Dawwen/PolyBoy/src/Psvita/sce_sys/livearea/contents/bg.png

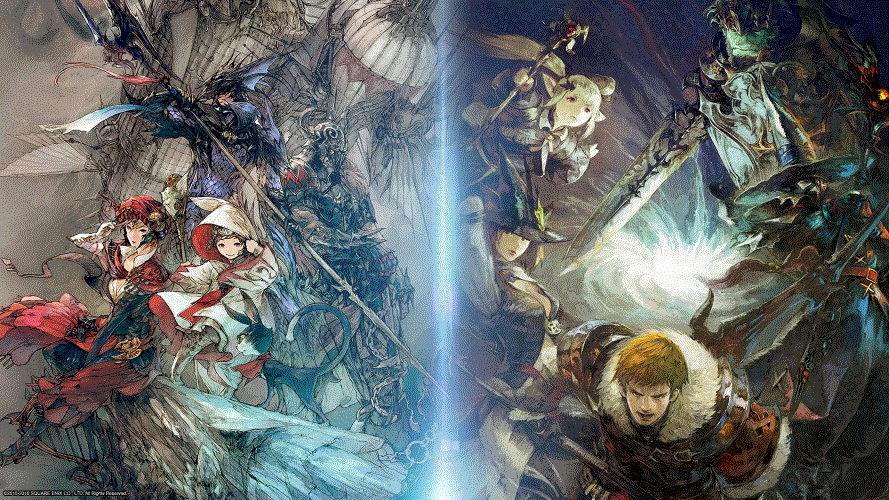
src/Psvita/sce_sys/livearea/contents/bg.png
