Dawwen/PolyBoy/src/Psvita/sce_sys/livearea/contents/startup.png

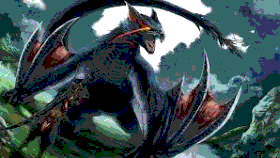
src/Psvita/sce_sys/livearea/contents/startup.png
