Dawwen/PolyBoy/models/Arduino Due/MicroUSB B - Hirose - ZX62D-B-5P8.SLDPRT

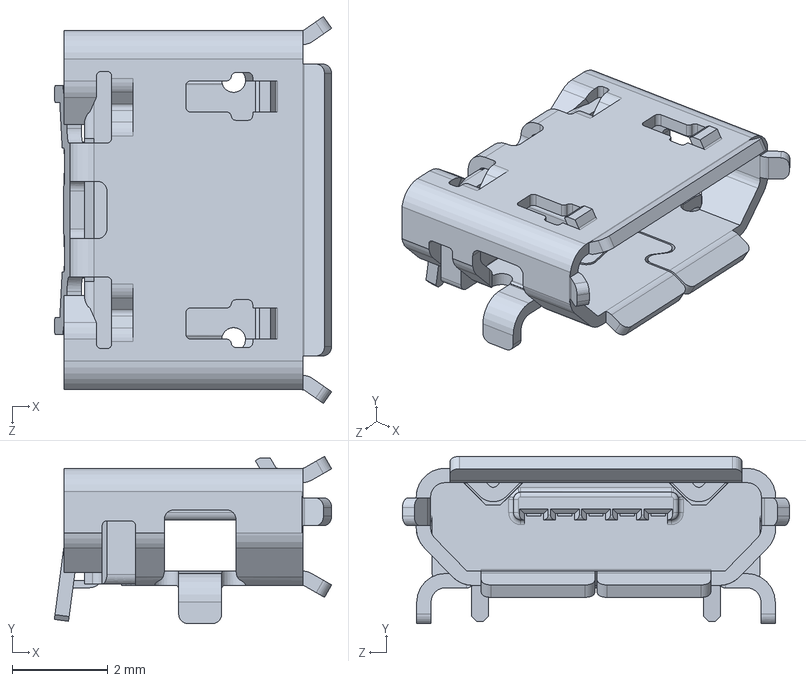
[picture p90: CAD file, 2021-04-26]
models/Arduino Due/MicroUSB B - Hirose - ZX62D-B-5P8.SLDPRT
5.80 x 3.50 x 8.09 mm
