Dawwen/PolyBoy/models/Entretoise10mm.SLDPRT

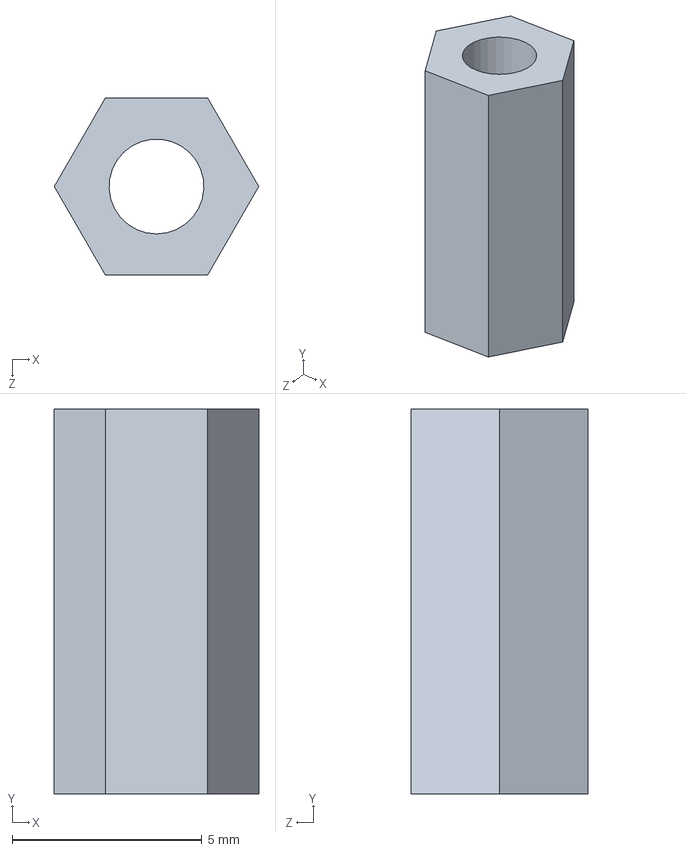
[picture p91: CAD file, 2021-04-26]
models/Entretoise10mm.SLDPRT
5.39 x 10.2 x 4.67 mm
