Dawwen/PolyBoy/models/Arduino Due/LED - Kingbright - KPT-3216EC.SLDPRT

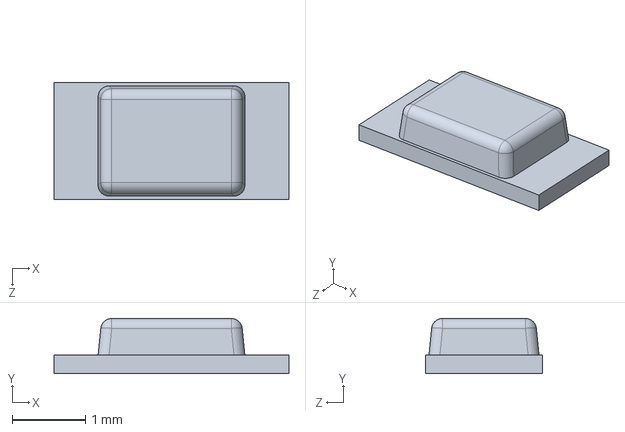
[picture p92: CAD file, 2021-04-26]
models/Arduino Due/LED - Kingbright - KPT-3216EC.SLDPRT
3.20 x 0.75 x 1.60 mm
