Dawwen/PolyBoy/models/PlaqueDPad.SLDPRT

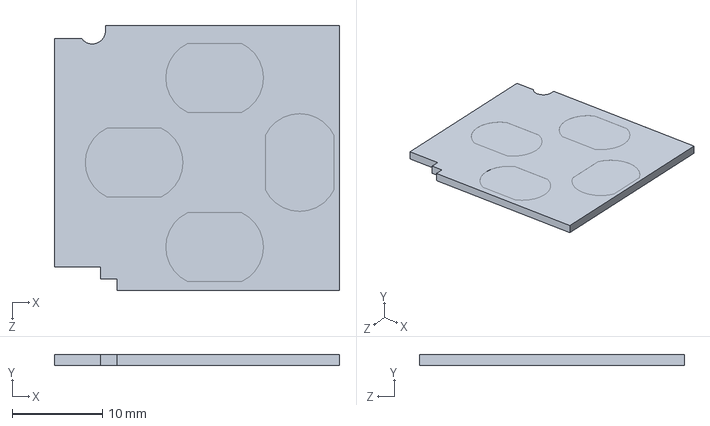
[picture p93: CAD file, 2021-04-26]
models/PlaqueDPad.SLDPRT
31.5 x 1.20 x 29.3 mm
