Dawwen/PolyBoy/models/Arduino Due/Switch - ESwitch - TLE3303.SLDPRT

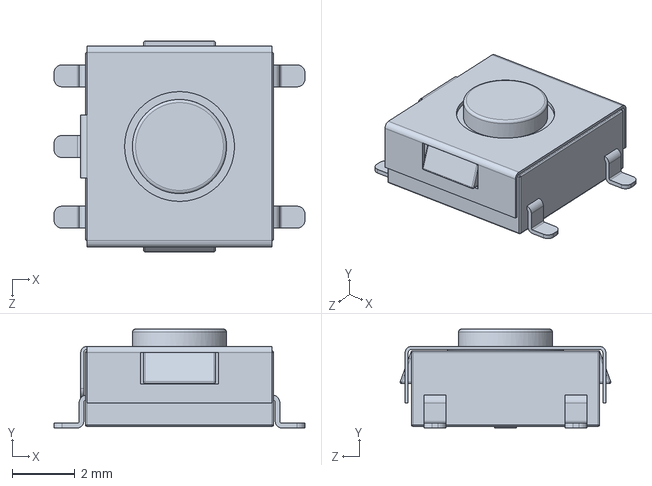
[picture p94: CAD file, 2021-04-26]
models/Arduino Due/Switch - ESwitch - TLE3303.SLDPRT
8.00 x 3.15 x 6.71 mm
