Dawwen/PolyBoy/models/BoitierHaut.SLDPRT

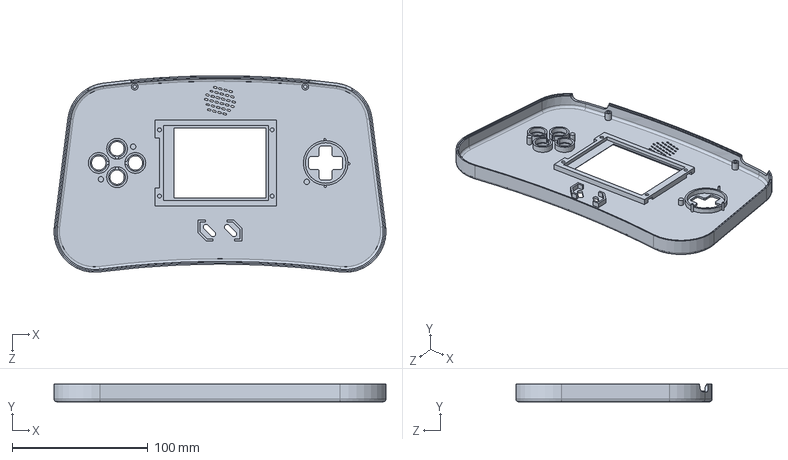
[picture p95: CAD file, 2021-04-26]
models/BoitierHaut.SLDPRT
245.0 x 13.0 x 145.0 mm
