Dawwen/PolyBoy/models/Arduino Due/Berg Header - 2.54 x 2.SLDPRT

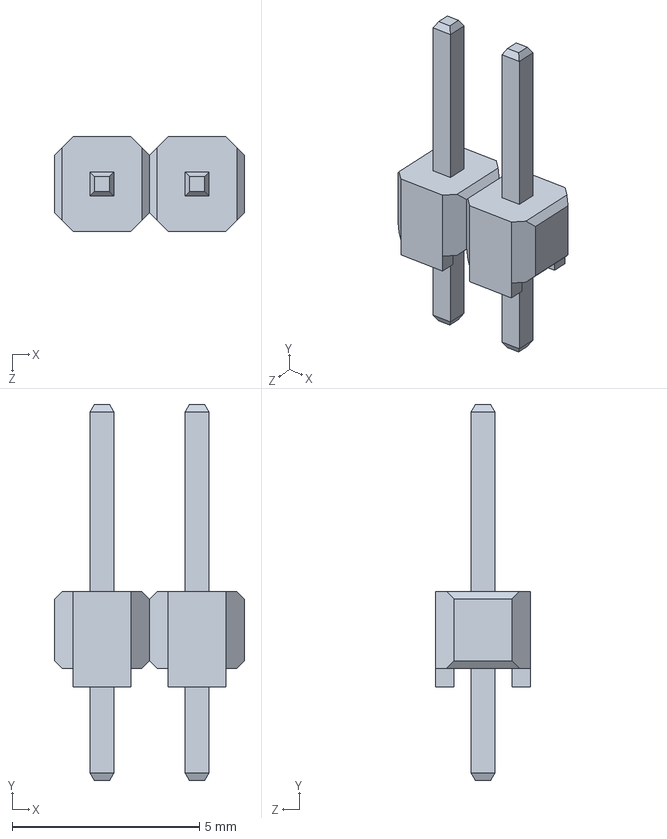
[picture p96: CAD file, 2021-04-26]
models/Arduino Due/Berg Header - 2.54 x 2.SLDPRT
5.08 x 10.0 x 2.54 mm
