Dawwen/PolyBoy/models/PlaqueGachette1.SLDPRT

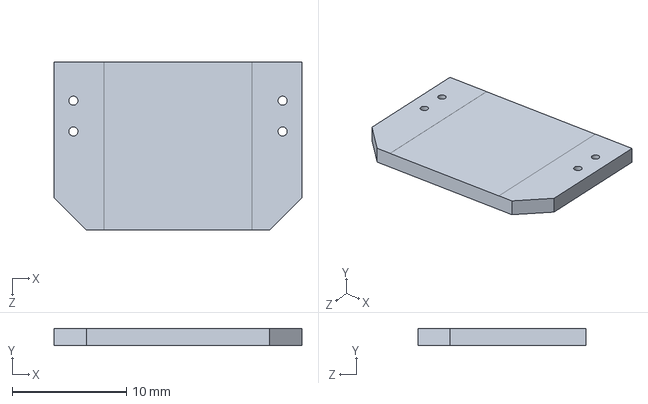
[picture p97: CAD file, 2021-04-26]
models/PlaqueGachette1.SLDPRT
21.8 x 1.50 x 14.8 mm
