Dawwen/PolyBoy/models/Arduino Due/MicroUSB AB - Hirose - ZX62D-AB-5P8.SLDPRT

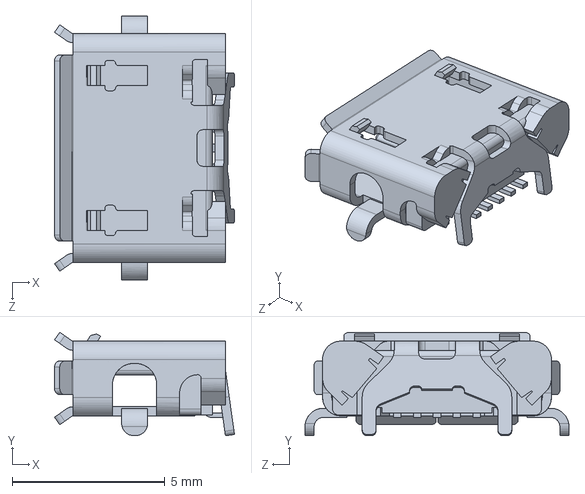
[picture p98: CAD file, 2021-04-26]
models/Arduino Due/MicroUSB AB - Hirose - ZX62D-AB-5P8.SLDPRT
5.90 x 3.39 x 8.65 mm
