Dawwen/PolyBoy/models/Entretoise8mm.SLDPRT

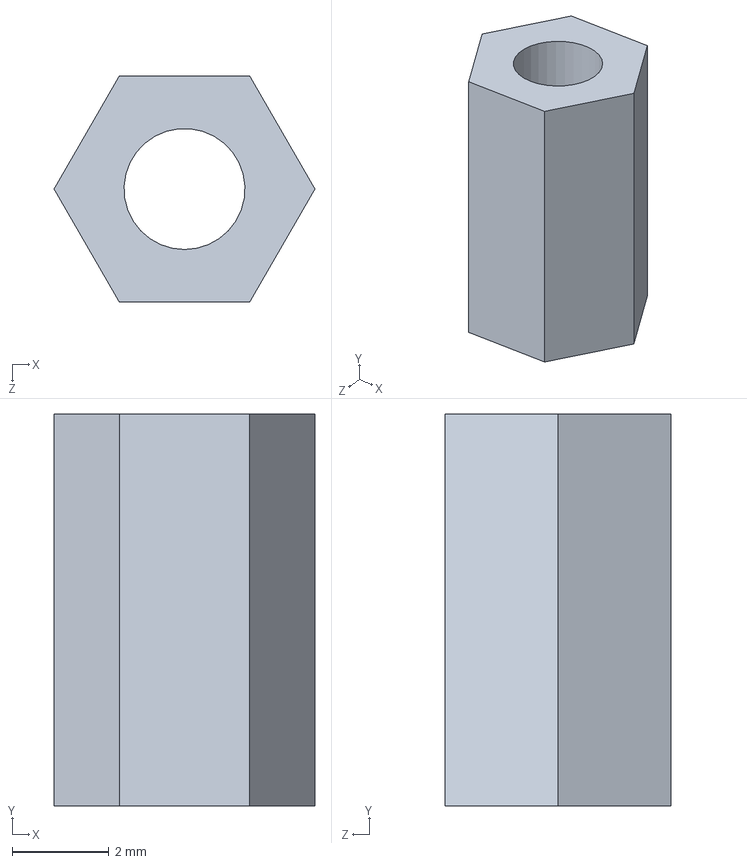
[picture p99: CAD file, 2021-04-26]
models/Entretoise8mm.SLDPRT
5.39 x 8.10 x 4.67 mm
