Dawwen/PolyBoy/models/Arduino Due/Berg Header Receptacle 2.54 x 10 - FCI - 66951-010LF.SLDPRT

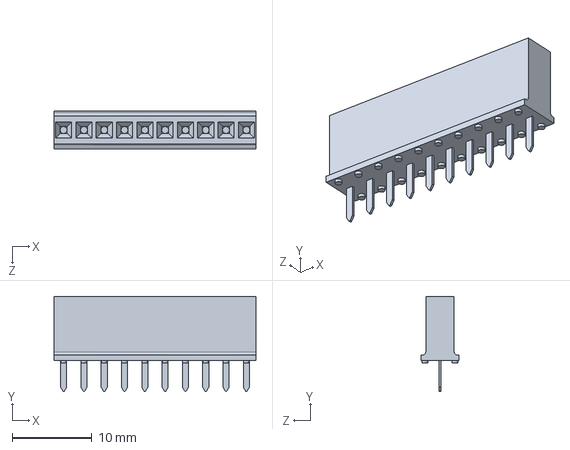
[picture p100: CAD file, 2021-04-26]
models/Arduino Due/Berg Header Receptacle 2.54 x 10 - FCI - 66951-010LF.SLDPRT
25.3 x 11.9 x 4.78 mm
