Dawwen/PolyBoy/models/PlaqueABXY.SLDPRT

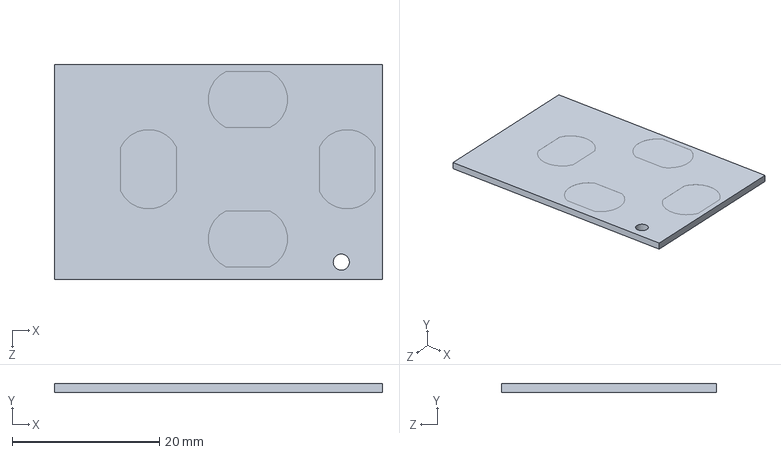
[picture p101: CAD file, 2021-04-26]
models/PlaqueABXY.SLDPRT
44.6 x 1.20 x 29.3 mm
