Dawwen/PolyBoy/models/Boulon.SLDPRT

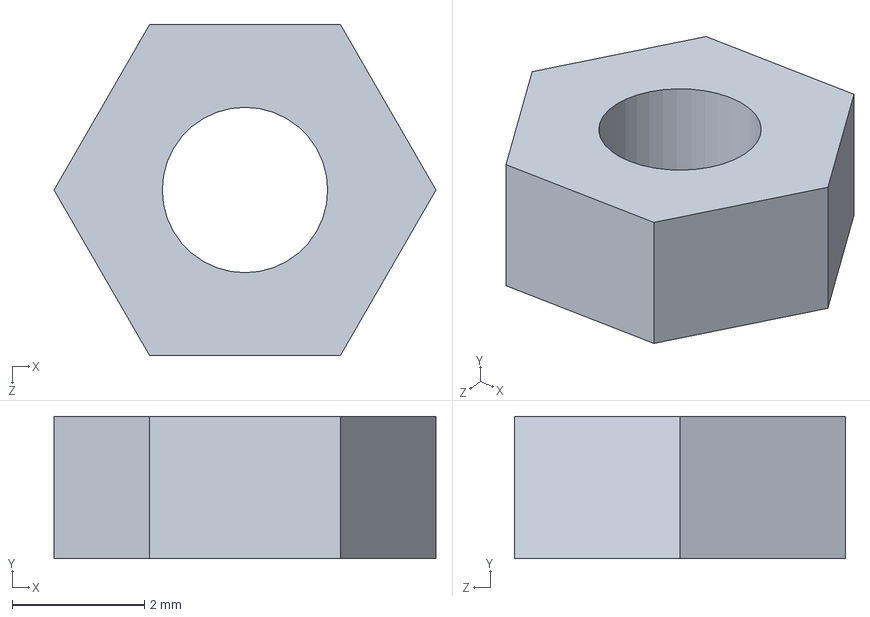
[picture p103: CAD file, 2021-04-26]
models/Boulon.SLDPRT
5.77 x 2.15 x 5.00 mm
