Dawwen/PolyBoy/models/Arduino Due/PCB - Arduino.SLDPRT

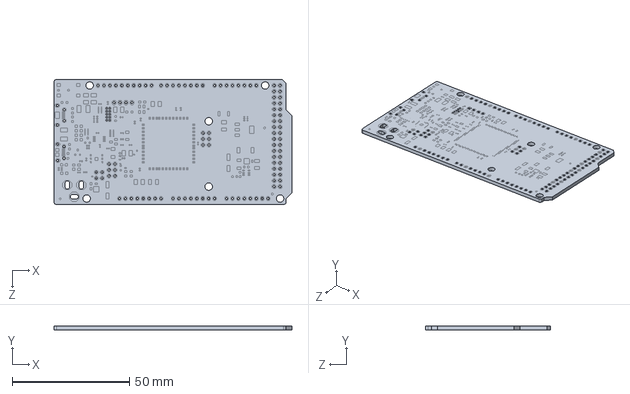
[picture p104: CAD file, 2021-04-26]
models/Arduino Due/PCB - Arduino.SLDPRT
101.6 x 1.62 x 53.3 mm
