Dawwen/PolyBoy/models/PlaqueStart.SLDPRT

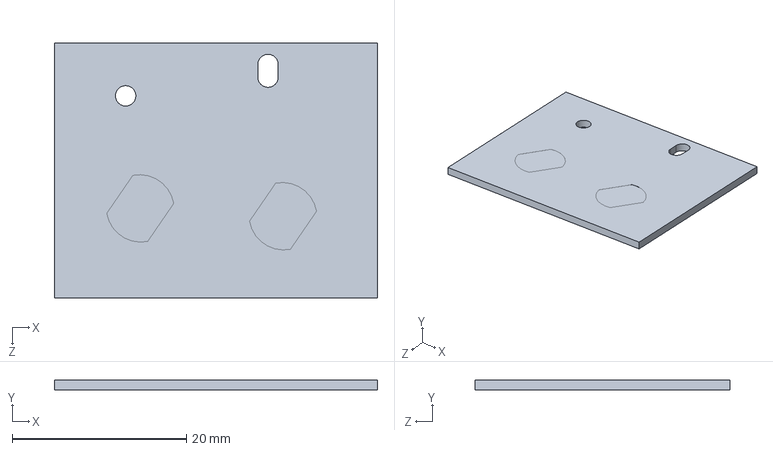
[picture p105: CAD file, 2021-04-26]
models/PlaqueStart.SLDPRT
37.1 x 1.20 x 29.3 mm
