Dawwen/PolyBoy/models/Arduino Due/Berg Header - 1.27 x 10.SLDPRT

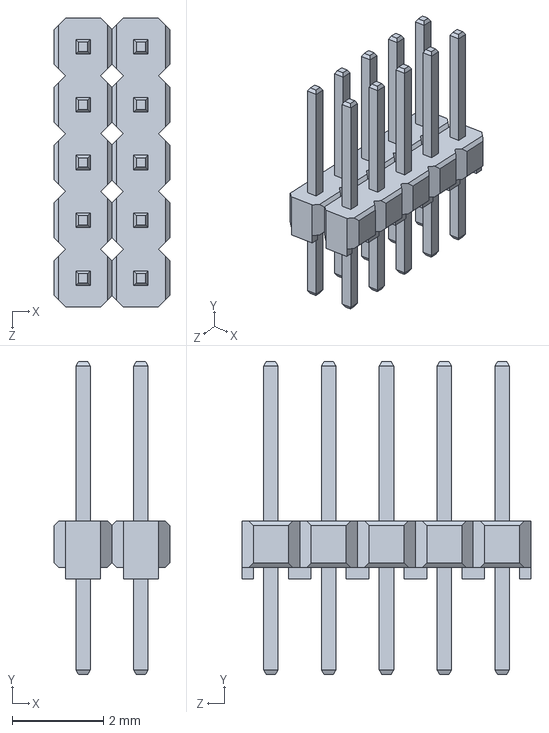
[picture p106: CAD file, 2021-04-26]
models/Arduino Due/Berg Header - 1.27 x 10.SLDPRT
2.54 x 6.88 x 6.35 mm
