Dawwen/PolyBoy/models/Vis14mm.SLDPRT

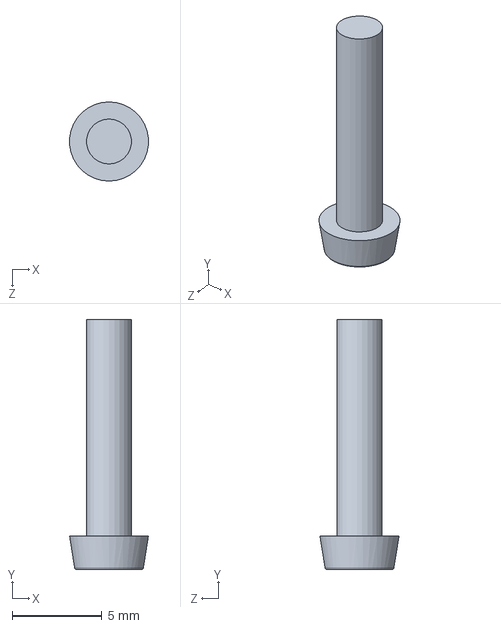
[picture p107: CAD file, 2021-04-26]
models/Vis14mm.SLDPRT
4.38 x 13.9 x 4.40 mm
