Dawwen/PolyBoy/models/MembraneDPad.SLDPRT

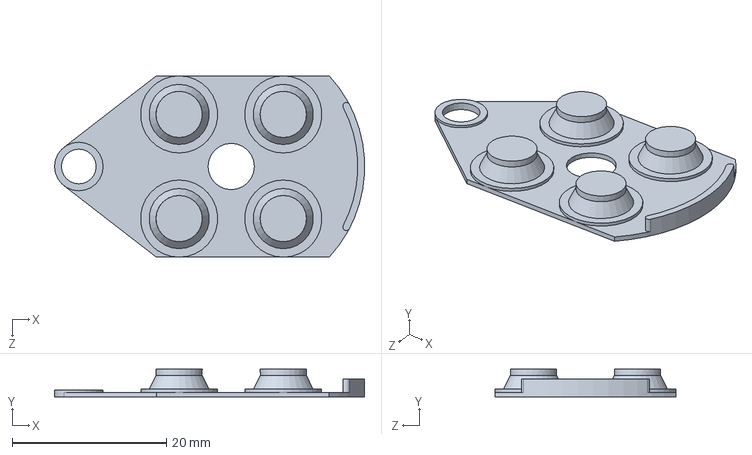
[picture p108: CAD file, 2021-04-26]
models/MembraneDPad.SLDPRT
40.2 x 3.60 x 23.5 mm
