Dawwen/PolyBoy/models/Entretoise20mm.SLDPRT

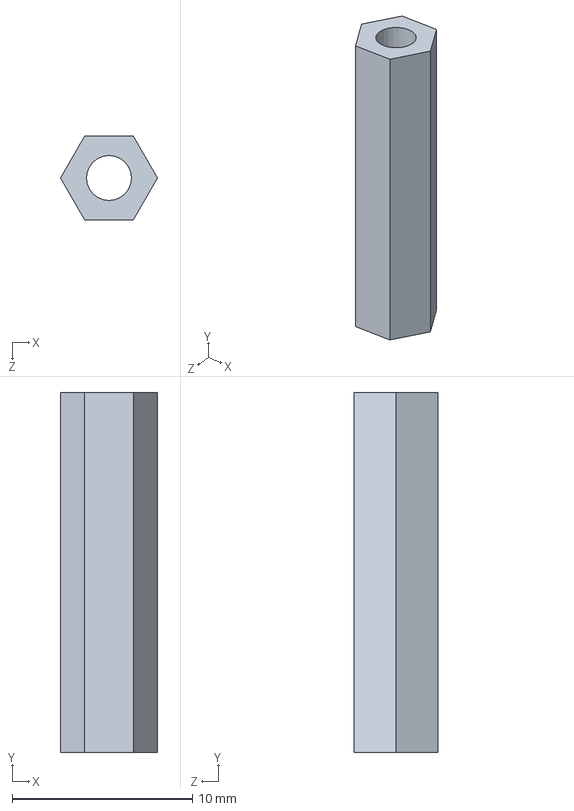
[picture p109: CAD file, 2021-04-26]
models/Entretoise20mm.SLDPRT
5.39 x 20.0 x 4.67 mm
