Dawwen/PolyBoy/models/Bouton.SLDPRT

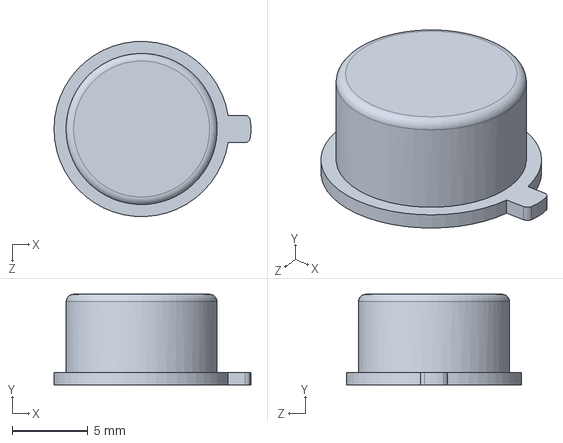
[picture p110: CAD file, 2021-04-26]
models/Bouton.SLDPRT
13.0 x 6.00 x 11.6 mm
