Dawwen/PolyBoy/models/PlaqueGachette2.SLDPRT

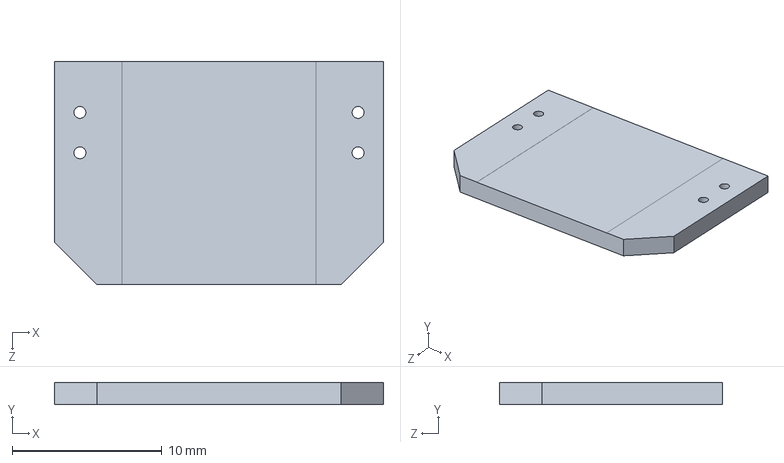
[picture p111: CAD file, 2021-04-26]
models/PlaqueGachette2.SLDPRT
22.0 x 1.50 x 14.9 mm
