Dawwen/PolyBoy/models/Entretoise12mm.SLDPRT

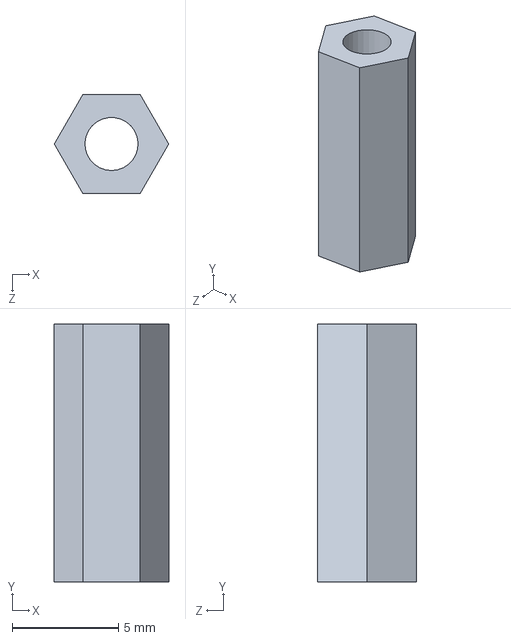
[picture p112: CAD file, 2021-04-26]
models/Entretoise12mm.SLDPRT
5.39 x 12.1 x 4.67 mm
