Dawwen/PolyBoy/models/Ecran.SLDPRT

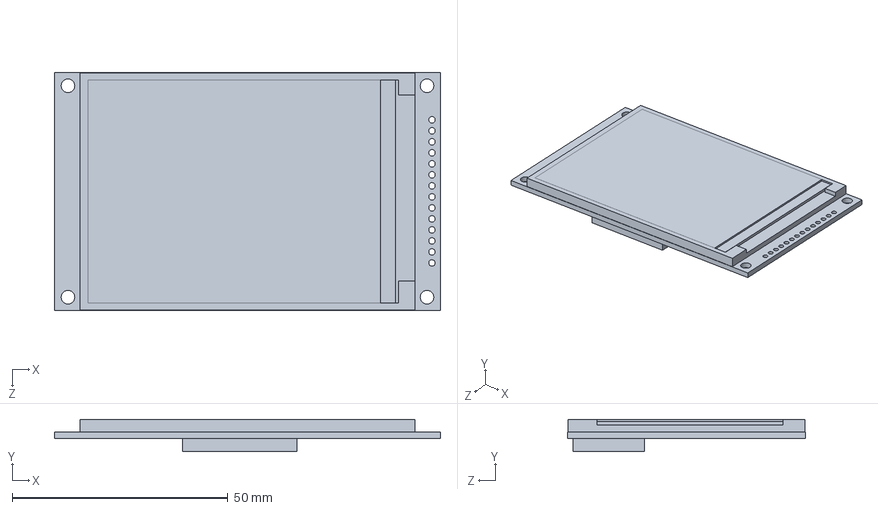
[picture p113: CAD file, 2021-04-26]
models/Ecran.SLDPRT
89.4 x 7.47 x 55.2 mm
