Dawwen/PolyBoy/models/MembraneABXY.SLDPRT

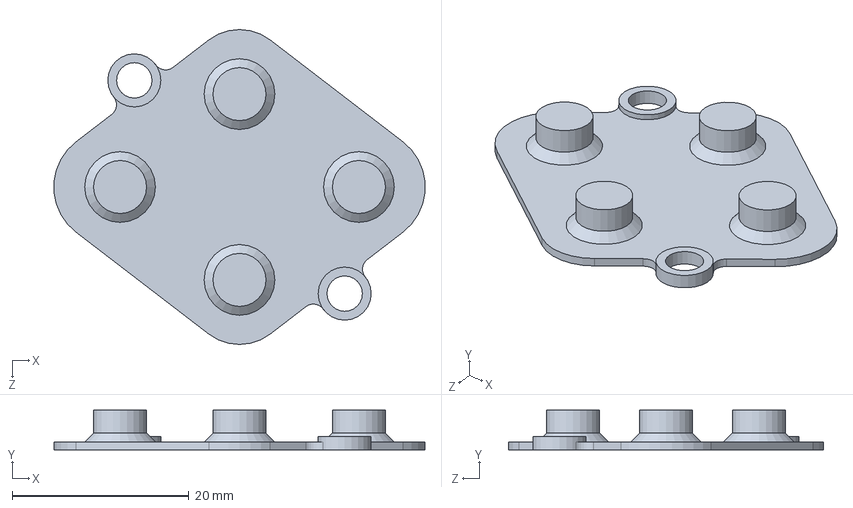
[picture p114: CAD file, 2021-04-26]
models/MembraneABXY.SLDPRT
41.9 x 4.50 x 35.6 mm
