Dawwen/PolyBoy/models/ModuleSD.SLDPRT

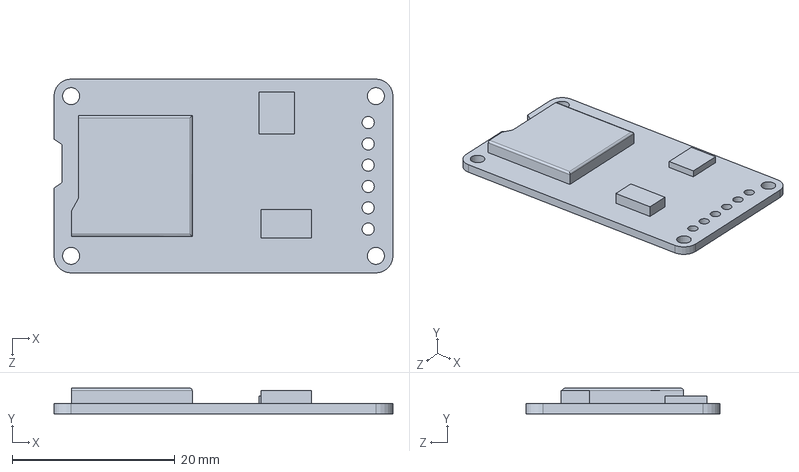
[picture p115: CAD file, 2021-04-26]
models/ModuleSD.SLDPRT
41.7 x 3.15 x 23.8 mm
