Dawwen/PolyBoy/models/Vis3.8mm.SLDPRT

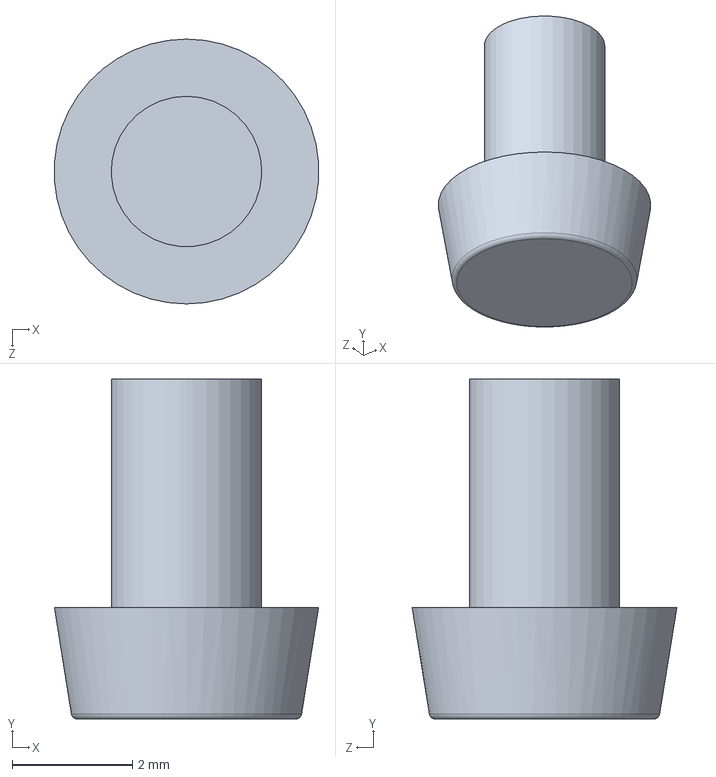
[picture p116: CAD file, 2021-04-26]
models/Vis3.8mm.SLDPRT
4.39 x 5.65 x 4.40 mm
