Dawwen/PolyBoy/models/BoitierBas.SLDPRT

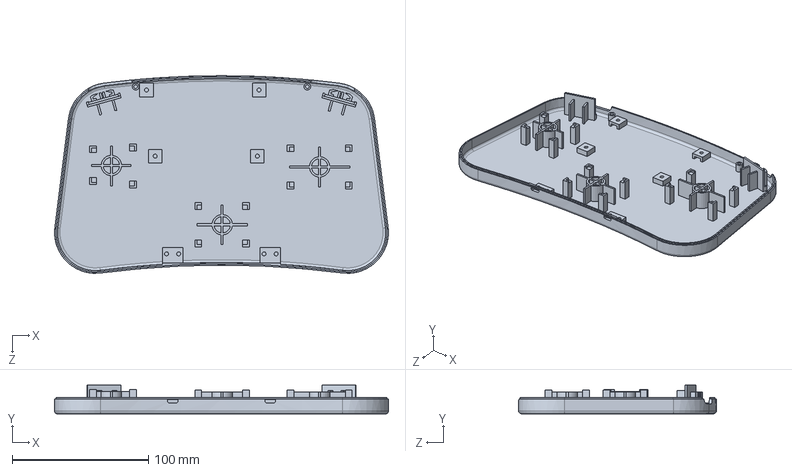
[picture p117: CAD file, 2021-04-26]
models/BoitierBas.SLDPRT
245.0 x 21.0 x 145.0 mm
