Dawwen/PolyBoy/models/Interrupteur.SLDPRT

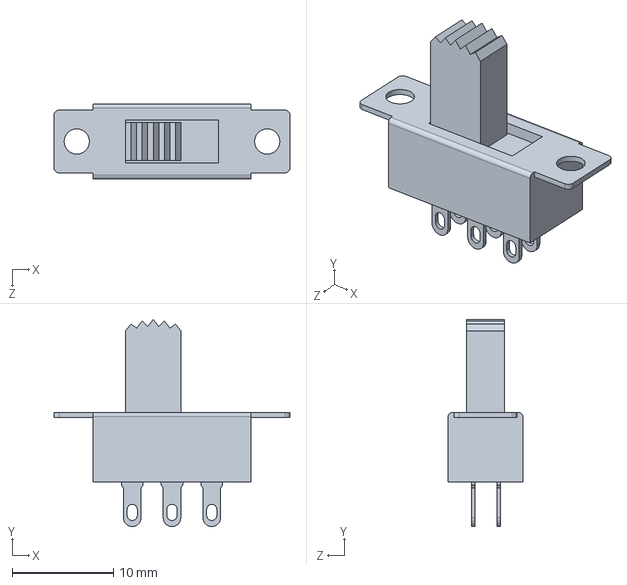
[picture p118: CAD file, 2021-04-26]
models/Interrupteur.SLDPRT
23.3 x 20.5 x 7.40 mm
