Dawwen/PolyBoy/models/Entretoise15mm.SLDPRT

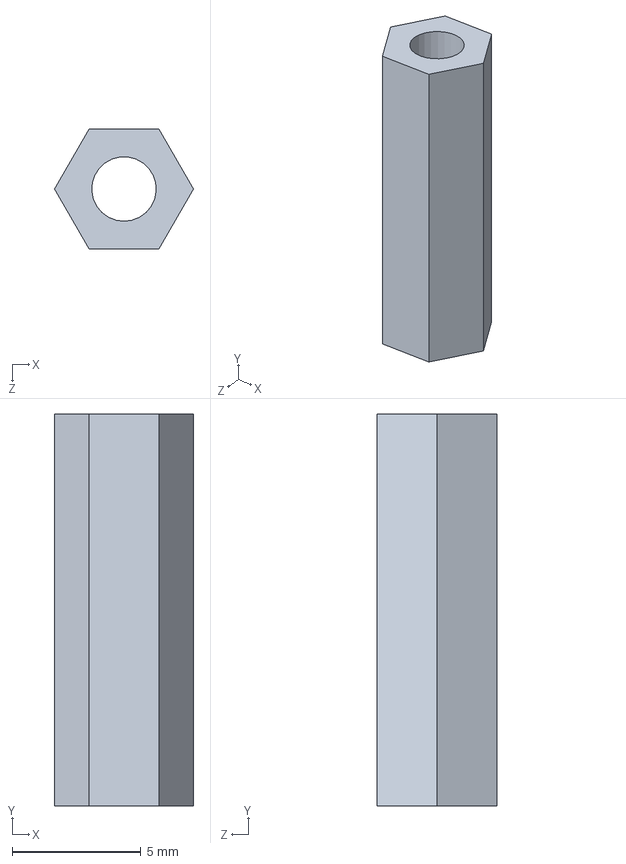
[picture p119: CAD file, 2021-04-26]
models/Entretoise15mm.SLDPRT
5.39 x 15.2 x 4.67 mm
