Dawwen/PolyBoy/models/Vis4mm.SLDPRT

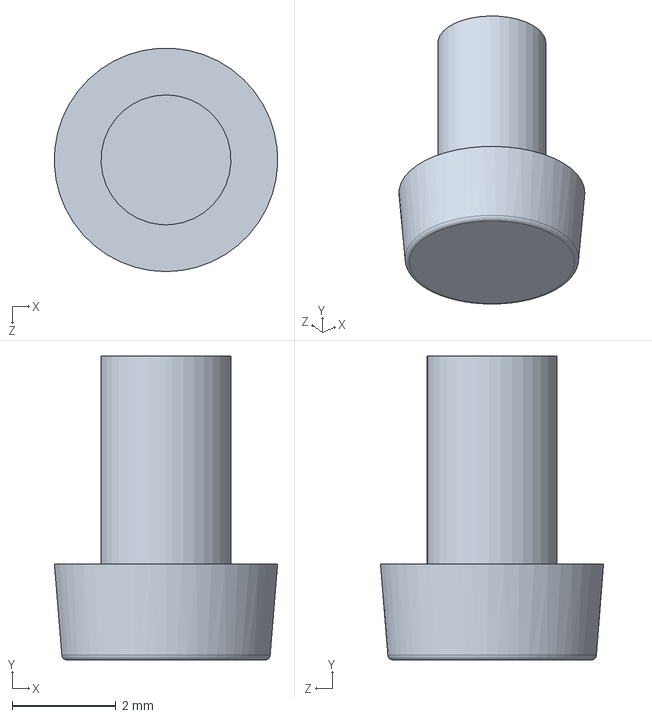
[picture p120: CAD file, 2021-04-26]
models/Vis4mm.SLDPRT
4.30 x 5.85 x 4.29 mm
