Dawwen/PolyBoy/models/Entretoise25mm.SLDPRT

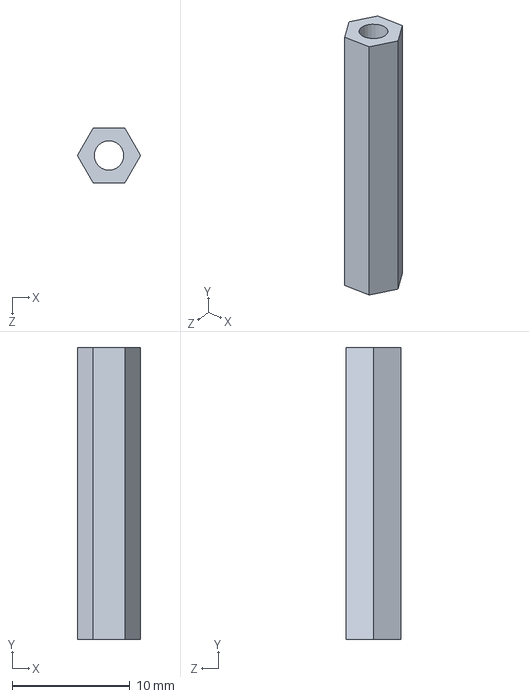
[picture p121: CAD file, 2021-04-26]
models/Entretoise25mm.SLDPRT
5.39 x 24.9 x 4.67 mm
