Dawwen/PolyBoy/models/DPad.SLDPRT

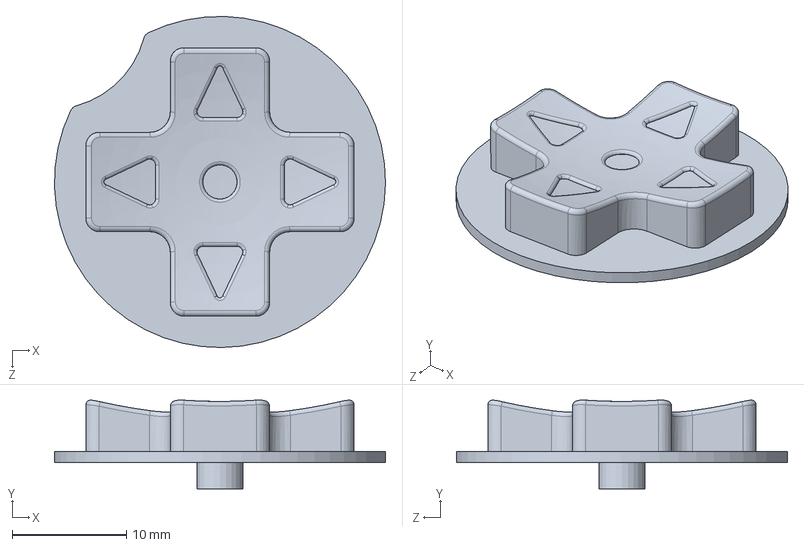
[picture p122: CAD file, 2021-04-26]
models/DPad.SLDPRT
29.0 x 7.79 x 29.0 mm
