Dawwen/PolyBoy/models/MembraneGachette.SLDPRT

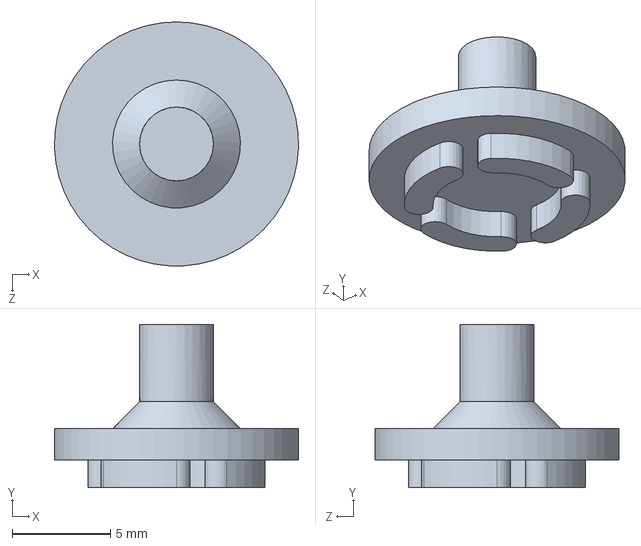
[picture p123: CAD file, 2021-04-26]
models/MembraneGachette.SLDPRT
12.4 x 8.30 x 12.4 mm
