Dawwen/PolyBoy/models/Vis8mm.SLDPRT

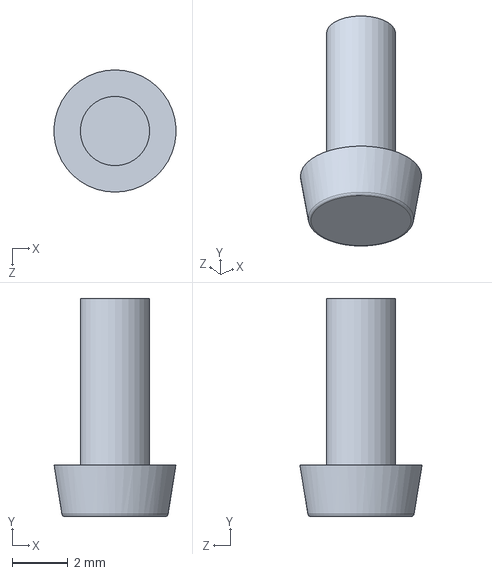
[picture p124: CAD file, 2021-04-26]
models/Vis8mm.SLDPRT
4.39 x 7.85 x 4.40 mm
